jsauermann/OmFLA/hardware/battery_J4.jpg

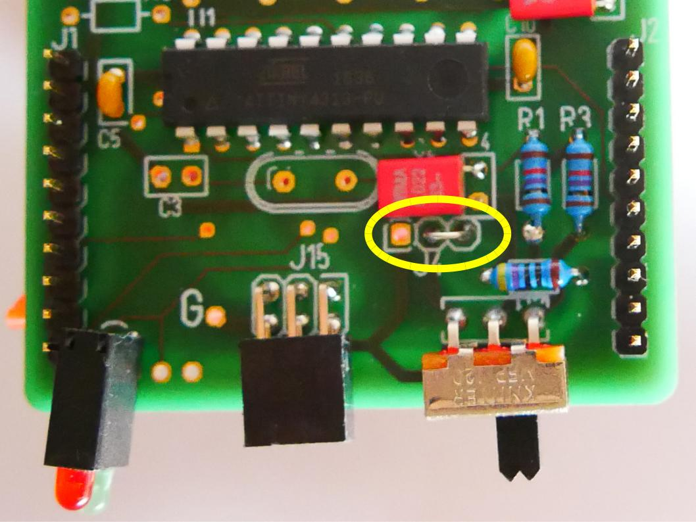
hardware/battery_J4.jpg
