jsauermann/OmFLA/hardware/battery_mounted.jpg

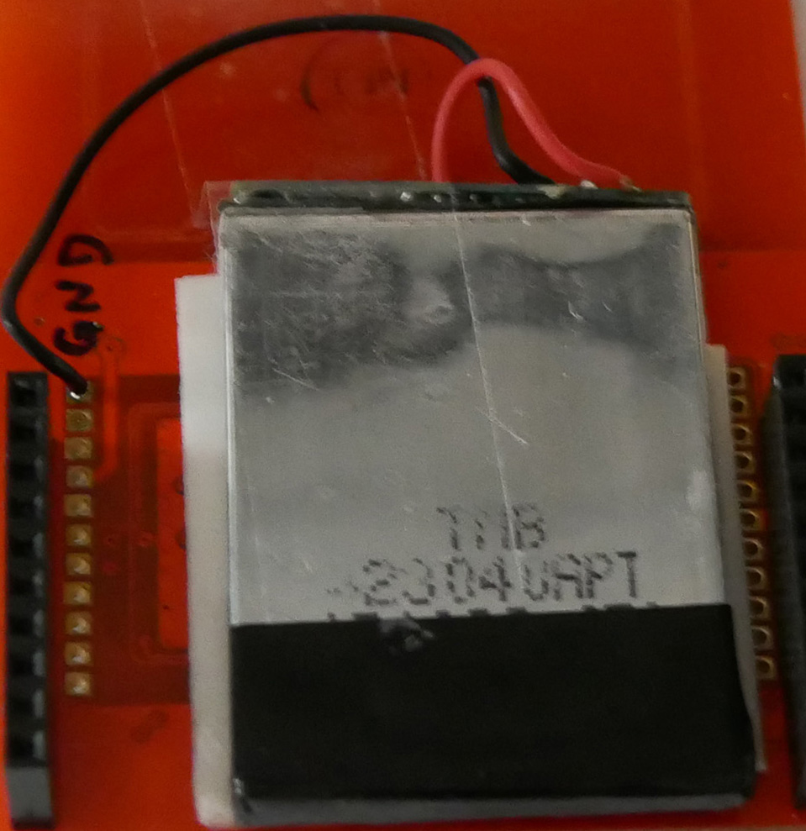
hardware/battery_mounted.jpg
