jsauermann/OmFLA/hardware/Bottom.jpg

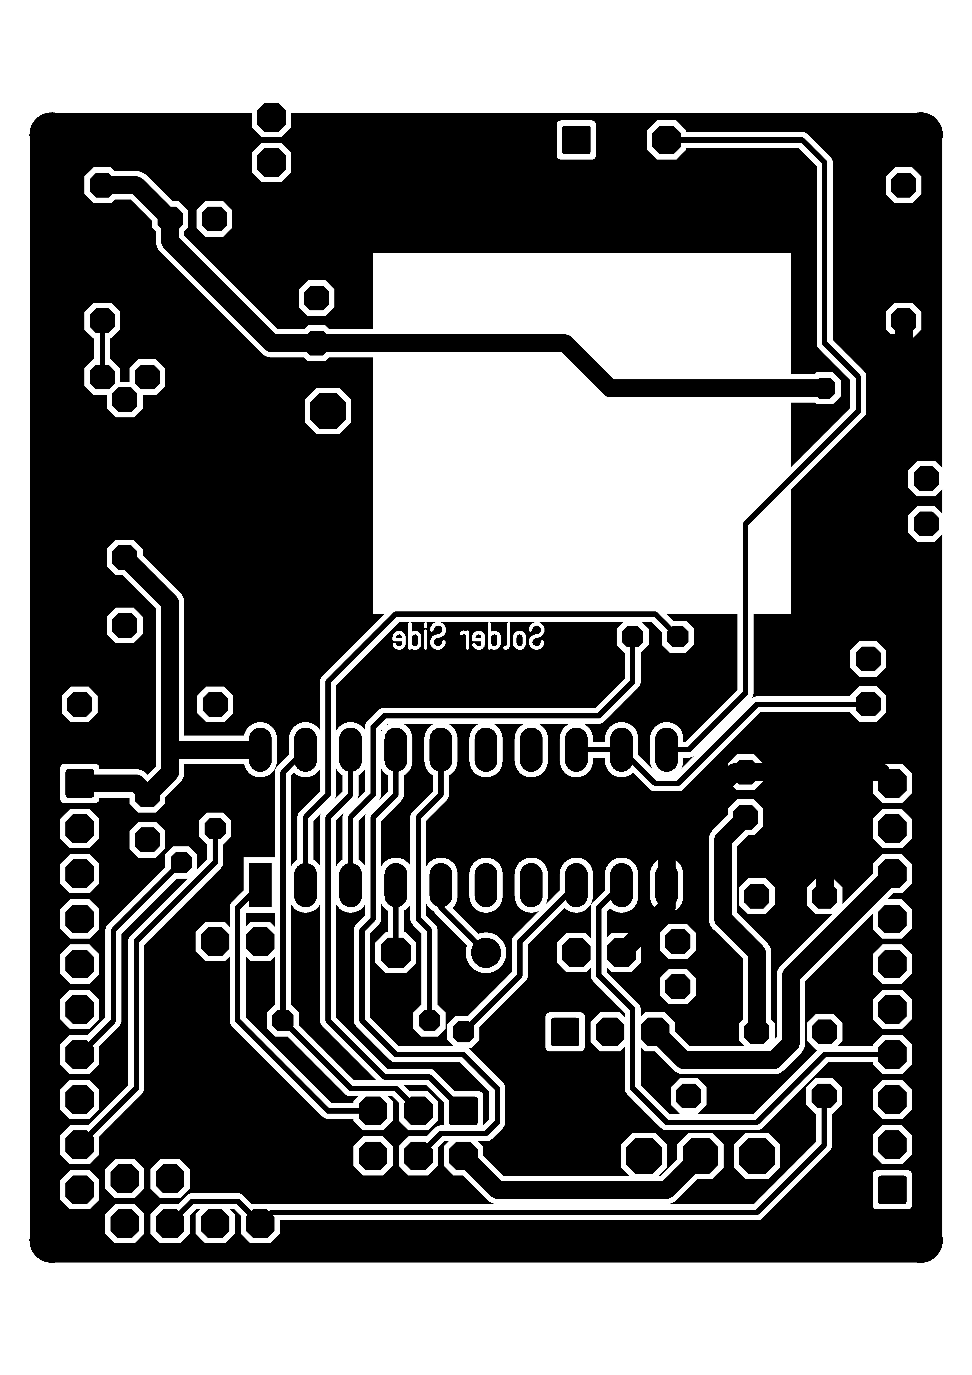
hardware/Bottom.jpg
