jsauermann/OmFLA/hardware/RFID-reader-after.jpg

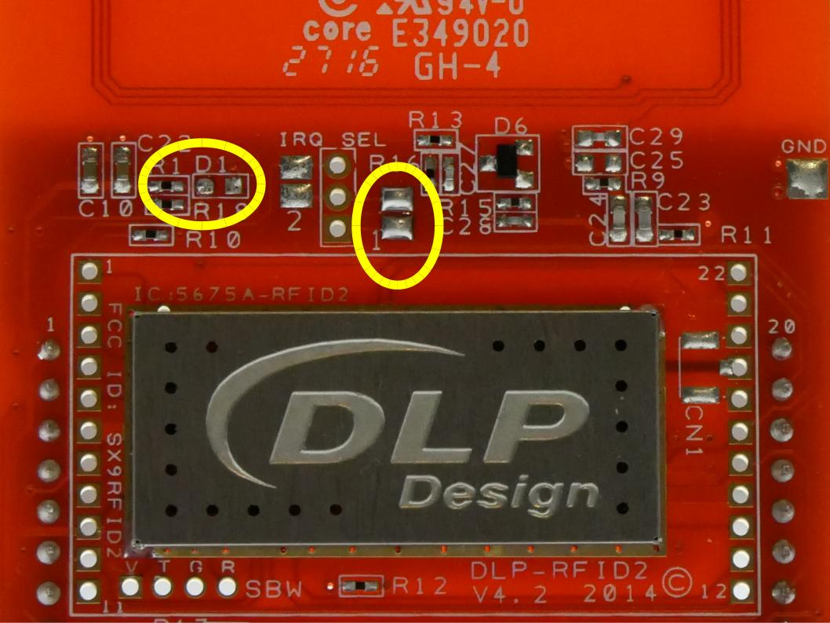
hardware/RFID-reader-after.jpg
