jsauermann/OmFLA/hardware/RFID-reader-before.jpg

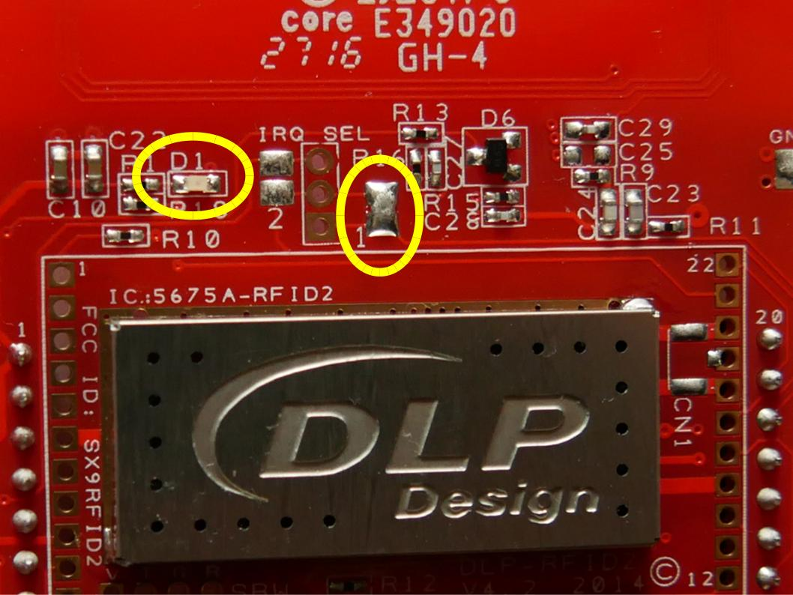
hardware/RFID-reader-before.jpg
