jsauermann/OmFLA/hardware/Schematics.jpg

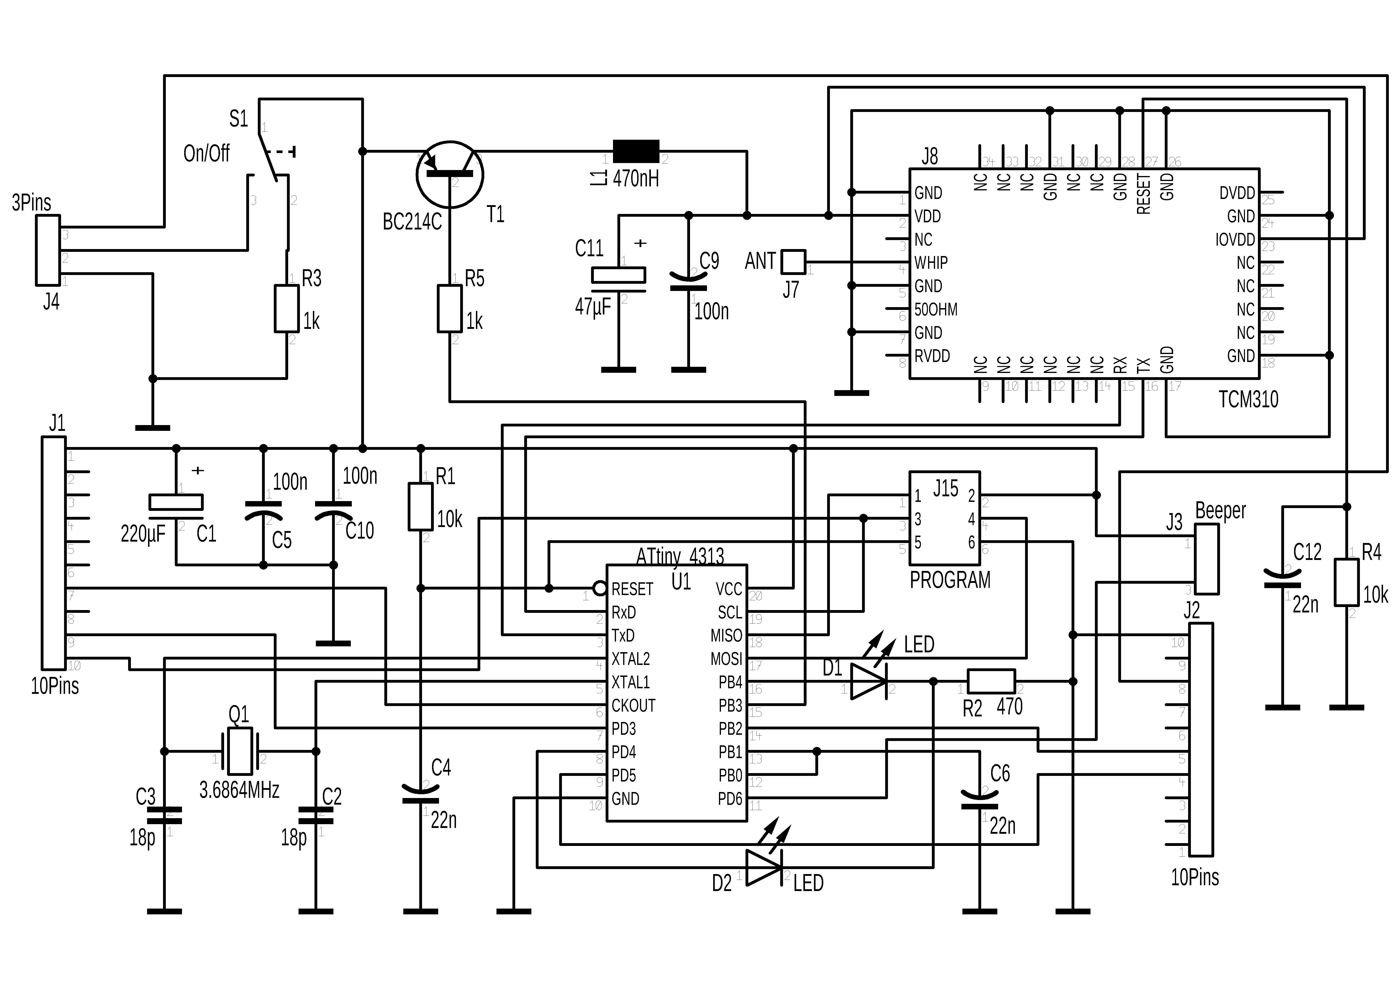
hardware/Schematics.jpg
