jsauermann/OmFLA/other_hardware/Schematics_1.jpg

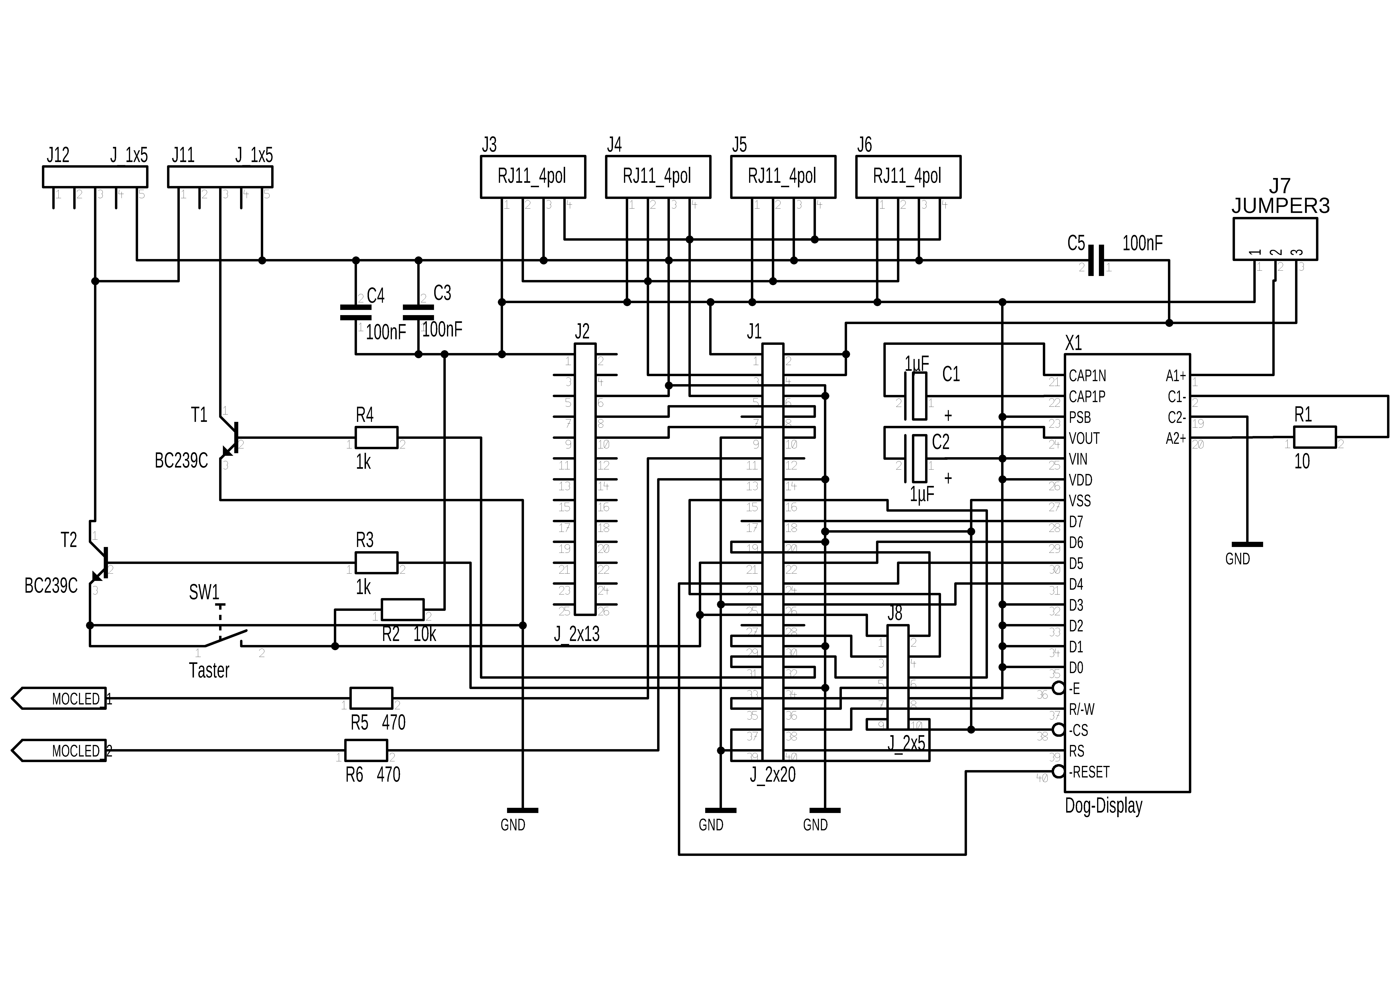
other_hardware/Schematics_1.jpg
