jsauermann/OmFLA/hardware/Components.jpg

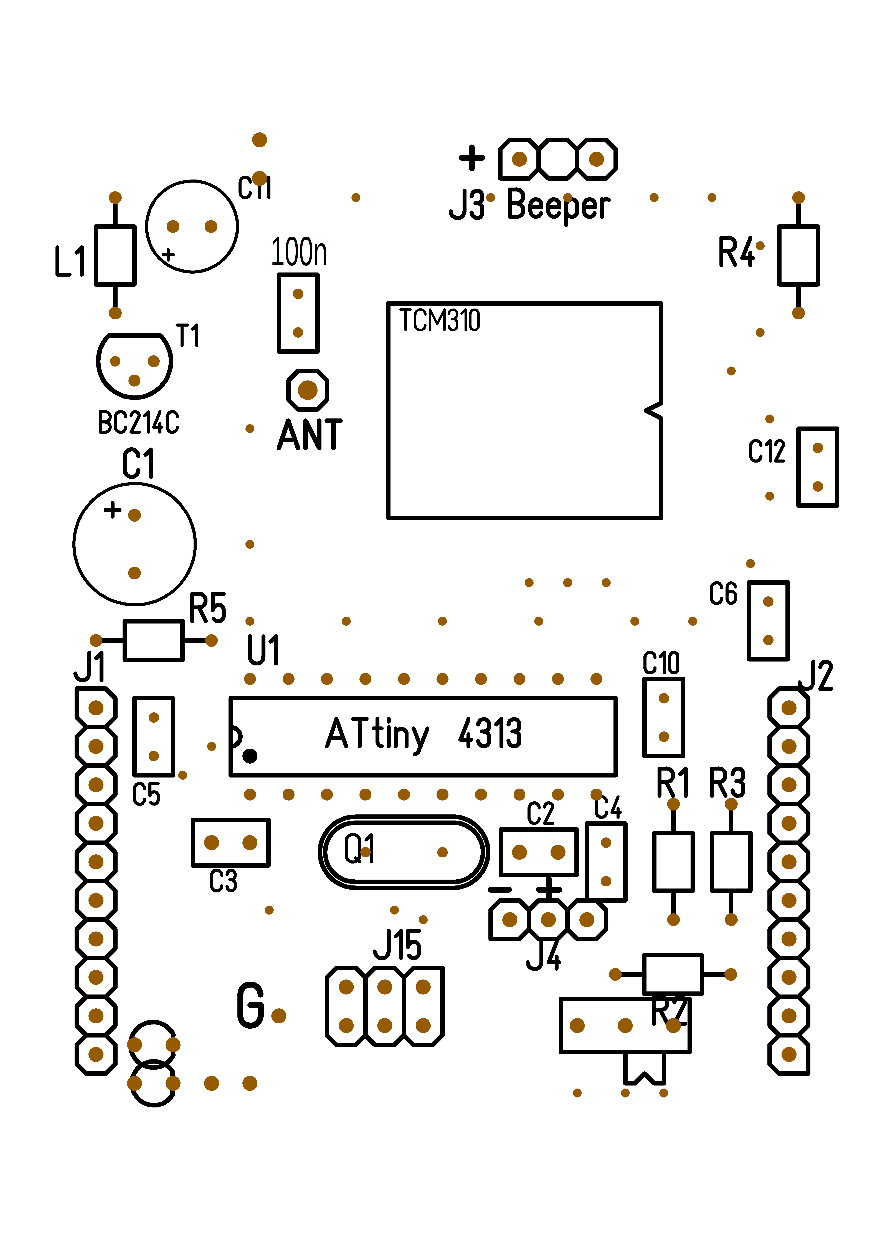
hardware/Components.jpg
